frivermen/qmk-trackball-60mm/photos/IMG_20260716_010507.jpg

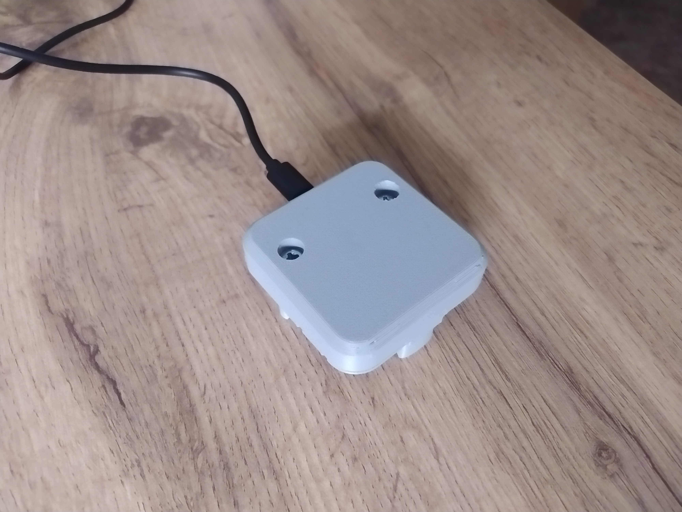
photos/IMG_20260716_010507.jpg
